engelberd/sensor-system/node/image/README-bootloader/1779827436513.png

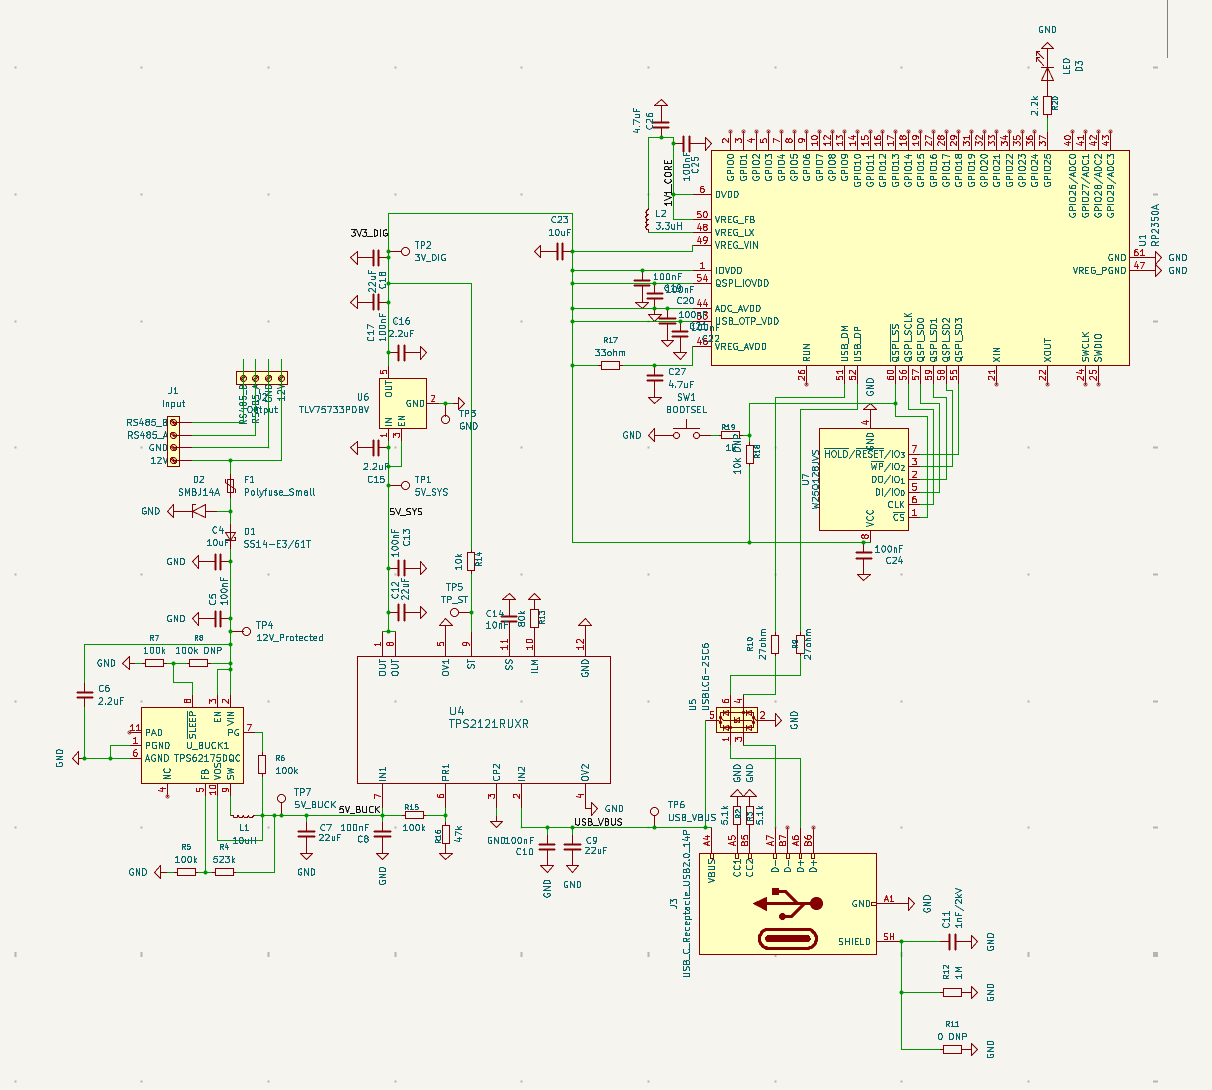
node/image/README-bootloader/1779827436513.png
