engelberd/sensor-system/node/adxl355/adxl355_driver.h

#pragma once

#include <cstddef>
#include <cstdint>

#include "hardware/sync.h"
#include "hardware/spi.h"

#include "common/sensor_types.h"
#include "interfaces/i_accelerometer.h"
#include "interfaces/i_temperature_sensor.h"
#include "timing/drdy_timestamp_ring.h"

class Adxl355Driver : public IAccelerometer, public ITemperatureSensor {
public:
    explicit Adxl355Driver(spi_inst_t* spi,
                           uint cs_pin,
                           int drdy_pin = -1,
                           int int1_pin = -1,
                           bool enable_sample_timestamps = false);

    SensorStatus init() override;
    SensorStatus check_device() override;
    SensorStatus configure(const AccelerometerConfig& config) override;
    SensorStatus read_sample(AccelSample& sample) override;
    SensorStatus read_fifo_samples(AccelSample* samples,
                                   size_t max_samples,
                                   size_t& samples_read) override;
    SensorStatus read_fifo_samples_timed(
        AccelSample* samples,
        SampleDeviceTime* times,
        size_t max_samples,
        size_t& samples_read
    ) override;

    bool supports_fifo() const override;
    bool supports_sample_timestamps() const override;
    void notify_fifo_timing_discontinuity(
        uint16_t quality_flags
    ) override;
    SensorStatus configure_fifo(uint8_t watermark) override;

    bool supports_data_ready_interrupt() const override;
    uint8_t consume_data_ready_event_sources() override;
    SensorStatus read_status(uint8_t& status) override;
    SensorStatus refresh_diagnostic_snapshot() override;
    SensorDiagnosticSnapshot diagnostic_snapshot() const override;

    SensorStatus set_offset(int32_t x, int32_t y, int32_t z) override;
    SensorStatus run_self_test(SelfTestResult& result) override;

    SensorStatus read_temperature(TemperatureSample& temperature) override;

    SensorStatus read_fifo_entries(uint8_t& entries) override;

private:
    struct FifoEntry {
        int32_t value = 0;
        bool is_x_axis = false;
        bool is_empty = false;
    };

private:
    spi_inst_t* spi_;
    uint cs_pin_;
    int drdy_pin_;
    int int1_pin_;
    bool initialized_ = false;
    bool sample_timestamps_enabled_ = false;
    uint8_t current_range_g_ = 2;
    SensorDiagnosticSnapshot diag_{};

    static Adxl355Driver* active_instance_;
    volatile uint8_t data_ready_sources_ = 0;
    bool int1_irq_enabled_ = false;
    bool drdy_irq_enabled_ = false;
    static constexpr size_t kDrdyTimestampCapacity = 512;
    DrdyTimestampRing<kDrdyTimestampCapacity> drdy_timestamps_{};
    uint64_t next_drdy_event_seq_ = 1;
    uint64_t last_consumed_drdy_event_seq_ = 0;
    uint32_t timing_segment_id_ = 1;
    volatile bool timing_binding_valid_ = false;
    volatile uint16_t timing_invalid_flags_ = TIMING_QUALITY_INVALID;

    static void gpio_irq_handler(uint gpio, uint32_t events);
    void disable_int1_irq();
    void enable_int1_irq();
    void clear_pending_irq_sources();
    void reset_timing_binding(uint16_t quality_flags, bool valid);
    void invalidate_timing_binding(uint16_t quality_flags);
    bool consume_fifo_timestamps(size_t consumed_samples,
                                 SampleDeviceTime* times,
                                 size_t valid_samples);

    

private:
    void cs_select();
    void cs_deselect();

    SensorStatus read_register(uint8_t reg, uint8_t& value);
    SensorStatus write_register(uint8_t reg, uint8_t value);
    SensorStatus read_multiple(uint8_t start_reg, uint8_t* buffer, size_t length);

    SensorStatus read_fifo_raw(uint8_t* buffer, size_t length);
    SensorStatus decode_fifo_entry(const uint8_t* data, FifoEntry& entry);
    int32_t decode_20bit_signed(uint8_t msb, uint8_t mid, uint8_t lsb_nibble);

    SensorStatus read_temperature_raw(uint16_t& temp_raw);
    SensorStatus read_shadow_registers(uint8_t* values, size_t length);

    SensorStatus reset_device();
    SensorStatus read_status_register(uint8_t& status);
    void capture_gpio_debug_levels();
    SensorStatus refresh_interrupt_debug_registers();

    SensorStatus set_self_test(bool st1, bool st2);
    SensorStatus read_average_sample(AccelSample& avg, size_t count);

    SensorStatus enter_standby();
    SensorStatus enter_measurement_mode();

    SensorStatus set_range_internal(uint8_t range_bits);
    SensorStatus set_odr_internal(uint8_t odr_bits);
    SensorStatus set_int1_active_high_internal();
    SensorStatus set_drdy_enabled_internal(bool enabled);
    SensorStatus set_hpf_disabled();
    SensorStatus set_hpf_corner_internal(uint8_t high_pass_corner);
    SensorStatus write_offset_axis(uint8_t reg_h, uint8_t reg_l, int32_t value_16bit);
};
