engelberd/sensor-system/host/host_console.py

#!/usr/bin/env python3
from __future__ import annotations

import sys
from pathlib import Path


PROJECT_ROOT = Path(__file__).resolve().parent.parent
if str(PROJECT_ROOT) not in sys.path:
    sys.path.insert(0, str(PROJECT_ROOT))

from host.console.app import main  # noqa: E402


if __name__ == "__main__":
    raise SystemExit(main())
