engelberd/sensor-system/node/transport/transport.h

#pragma once

#include <cstddef>
#include <cstdint>
#include <cstring>

#include "common/protocol_ids.h"
#include "interfaces/i_data_plane.h"
#include "pico/stdlib.h"
#include "system/runtime_context.h"
#include "transport/frame_decoder.h"
#include "transport/frame_encoder.h"
#include "transport/frame_layout.h"
#include "transport/rs485_port.h"

template <size_t BufferCapacity, typename ControllerT>
class Transport {
public:
    static constexpr size_t MAX_FRAME_SIZE =
        FRAME_HEADER_SIZE + FRAME_MAX_PAYLOAD_SIZE + FRAME_CRC_SIZE;
    static constexpr size_t RX_BUFFER_SIZE = MAX_FRAME_SIZE;
    static constexpr size_t TX_FRAME_BUFFER_SIZE = MAX_FRAME_SIZE;
    static constexpr size_t RESPONSE_PAYLOAD_BUFFER_SIZE = FRAME_MAX_PAYLOAD_SIZE;
    static constexpr size_t MAX_PENDING_RESPONSES = 4;

    Transport(Rs485Port& port,
              ControllerT& controller,
              IDataPlane& data_plane,
              volatile uint8_t* requested_action = nullptr,
              uint64_t boot_epoch = 0,
              bool time_sync_enabled = false)
        : port_(port),
          controller_(controller),
          data_plane_(data_plane),
          requested_action_(requested_action),
          boot_epoch_(boot_epoch),
          time_sync_enabled_(time_sync_enabled && boot_epoch != 0) {
    }

    bool init() {
        rx_size_ = 0;
        tx_seq_ = 1;
        tx_kind_ = TxKind::None;
        pending_response_head_ = 0;
        pending_response_tail_ = 0;
        pending_response_count_ = 0;
        return true;
    }

    void update() {
        port_.poll();
        handle_tx_completion();
        process_rx();
        process_tx();
    }

private:
    static constexpr uint8_t kMagicLo =
        static_cast<uint8_t>(FRAME_MAGIC & 0xFFu);
    static constexpr uint8_t kMagicHi =
        static_cast<uint8_t>((FRAME_MAGIC >> 8) & 0xFFu);

    enum class TxKind : uint8_t {
        None = 0,
        Response,
        BurstData
    };

    using DeferredActionT = typename ControllerT::DeferredAction;

    void handle_tx_completion() {
        if (tx_kind_ == TxKind::None) {
            return;
        }

        if (port_.tx_busy()) {
            return;
        }

        if (!port_.tx_completed()) {
            return;
        }

        port_.clear_tx_completed();

        if (tx_kind_ == TxKind::BurstData) {
            data_plane_.on_packet_transmitted();
        } else if (tx_kind_ == TxKind::Response) {
            execute_deferred_action(active_response_action_, active_response_baudrate_);
            active_response_action_ = DeferredActionT::None;
            active_response_baudrate_ = 0;
        }

        tx_kind_ = TxKind::None;
    }

    void process_rx() {
        uint8_t byte = 0;

        while (port_.read_byte(byte)) {
            if (rx_size_ >= RX_BUFFER_SIZE) {
                rx_size_ = 0;
            }

            rx_buffer_[rx_size_++] = byte;

            align_rx_buffer_to_magic();

            while (true) {
                if (rx_size_ < FRAME_HEADER_SIZE) {
                    break;
                }

                FrameHeader header{};
                std::memcpy(&header, rx_buffer_, sizeof(header));

                if (header.version != FRAME_PROTOCOL_VERSION) {
                    discard_rx_prefix(1);
                    continue;
                }

                if (header.length > FRAME_MAX_PAYLOAD_SIZE) {
                    discard_rx_prefix(1);
                    continue;
                }

                const size_t expected_size =
                    FRAME_HEADER_SIZE +
                    static_cast<size_t>(header.length) +
                    FRAME_CRC_SIZE;

                if (expected_size > RX_BUFFER_SIZE) {
                    discard_rx_prefix(1);
                    continue;
                }

                if (rx_size_ < expected_size) {
                    break;
                }

                if (!try_decode_one_frame(expected_size)) {
                    // decode failed and buffer was resynced; try again
                    continue;
                }

                // one frame consumed successfully; maybe another one is already buffered
            }
        }
    }

    bool try_decode_one_frame(size_t frame_size) {
        DecodedFrame frame{};
        const auto st = decoder_.decode(rx_buffer_, frame_size, frame);

        if (st != FrameDecodeStatus::Ok) {
            discard_rx_prefix(1);
            align_rx_buffer_to_magic();
            return false;
        }

        handle_frame(frame, time_us_64());
        discard_rx_prefix(frame_size);
        align_rx_buffer_to_magic();
        return true;
    }

    void execute_deferred_action(DeferredActionT action, uint32_t deferred_baudrate) {
        if (action == DeferredActionT::None) {
            return;
        }

        if (action == DeferredActionT::ApplyBaudRate) {
            if (deferred_baudrate != 0) {
                port_.set_baudrate(deferred_baudrate);
            }
            return;
        }

        if (requested_action_ == nullptr) {
            return;
        }

        if (action == DeferredActionT::EnterBootloader) {
            *requested_action_ = RuntimeSystemActionEnterBootloader;
        } else if (action == DeferredActionT::Restart) {
            *requested_action_ = RuntimeSystemActionRestart;
        }
    }

    void handle_frame(const DecodedFrame& frame, uint64_t t2_node_rx_us) {
        if (frame.type != FrameType::Command) {
            return;
        }

        // Runtime commands must originate from the host; ignore node-to-node or echo artifacts.
        if (frame.source != HOST_NODE_ID) {
            return;
        }

        if (frame.payload == nullptr || frame.payload_length < 1) {
            return;
        }

        const bool directed_to_node = frame.destination == controller_.node_id();
        const bool accepted_broadcast =
            frame.destination == BROADCAST_NODE_ID &&
            controller_.accepts_broadcast_command(frame.payload, frame.payload_length);
        if (!directed_to_node && !accepted_broadcast) {
            return;
        }

        uint8_t response_payload[RESPONSE_PAYLOAD_BUFFER_SIZE]{};
        size_t response_payload_len = 0;

        const uint8_t cmd = frame.payload[0];

        if (time_sync_enabled_ &&
            cmd == static_cast<uint8_t>(CommandType::TimeSync)) {
            (void)queue_time_sync_response(frame, t2_node_rx_us);
            return;
        }

        const StatusCode st = controller_.handle_command(
            cmd,
            frame.source,
            frame.payload,
            frame.payload_length,
            response_payload,
            response_payload_len
        );

        if (response_payload_len == 0 && st == StatusCode::NoData) {
            return;
        }

        // Jeśli kontroler nie zbudował payloadu dla błędu, dobuduj minimalny nagłówek.
        if (response_payload_len == 0) {
            if (sizeof(ResponsePayloadHeader) <= sizeof(response_payload)) {
                ResponsePayloadHeader resp{};
                resp.command = cmd;
                resp.status = static_cast<uint8_t>(st);
                std::memcpy(response_payload, &resp, sizeof(resp));
                response_payload_len = sizeof(resp);
            } else {
                return;
            }
        }

        if (!queue_response(
                frame.source,
                controller_.node_id(),
                frame.sequence,
                response_payload,
                response_payload_len,
                controller_.take_deferred_action(),
                controller_.take_deferred_baudrate())) {
            (void)st;
        }
    }

    bool queue_response(uint8_t destination,
                        uint8_t source,
                        uint32_t sequence,
                        const uint8_t* payload,
                        size_t payload_len,
                        DeferredActionT deferred_action,
                        uint32_t deferred_baudrate) {
        if (payload == nullptr || payload_len == 0) {
            return false;
        }

        if (pending_response_count_ >= MAX_PENDING_RESPONSES) {
            return false;
        }

        PendingResponseSlot& slot = pending_response_queue_[pending_response_tail_];
        const size_t frame_len = encoder_.encode_response_frame_to(
            destination,
            source,
            sequence,
            0,
            payload,
            static_cast<uint16_t>(payload_len),
            slot.frame,
            sizeof(slot.frame)
        );

        if (frame_len == 0) {
            return false;
        }

        slot.frame_len = frame_len;
        slot.deferred_action = deferred_action;
        slot.deferred_baudrate = deferred_baudrate;
        pending_response_tail_ =
            (pending_response_tail_ + 1) % MAX_PENDING_RESPONSES;
        ++pending_response_count_;
        return true;
    }

    bool queue_time_sync_response(const DecodedFrame& frame,
                                  uint64_t t2_node_rx_us) {
        if (pending_response_count_ >= MAX_PENDING_RESPONSES) {
            return false;
        }

        TimeSyncResponsePayload response{};
        response.command = static_cast<uint8_t>(CommandType::TimeSync);
        response.version = 1;
        response.boot_epoch = boot_epoch_;
        response.t2_node_rx_us = t2_node_rx_us;

        if (frame.payload == nullptr ||
            frame.payload_length != sizeof(TimeSyncCommandPayload)) {
            response.status = static_cast<uint8_t>(StatusCode::InvalidParam);
        } else {
            TimeSyncCommandPayload request{};
            std::memcpy(&request, frame.payload, sizeof(request));
            response.sync_id = request.sync_id;
            response.echoed_t1_host_monotonic_ns =
                request.t1_host_monotonic_ns;
            response.status = static_cast<uint8_t>(
                request.version == 1
                    ? StatusCode::Ok
                    : StatusCode::Unsupported
            );
        }
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
